tg257225-oss/TKL-Keyboard/Assets/new usb receptacle.png

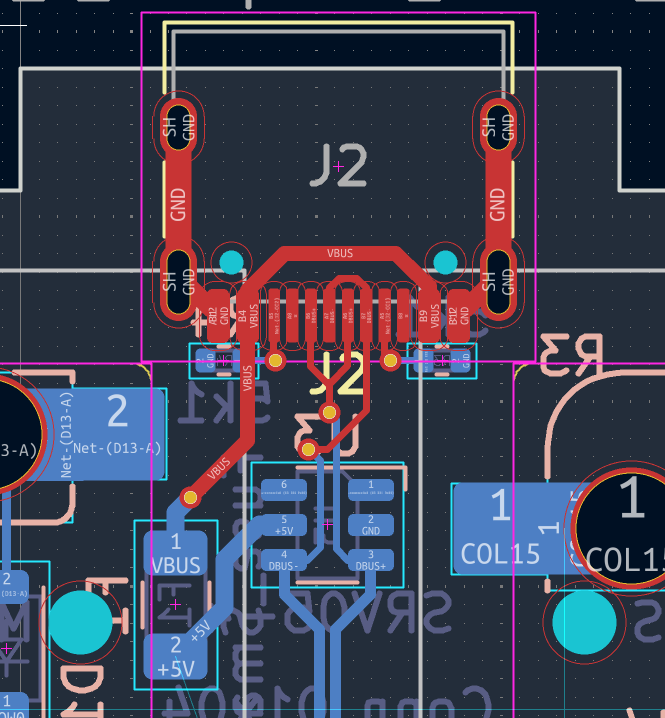
Assets/new usb receptacle.png
