tg257225-oss/TKL-Keyboard/Assets/plate sketch.png

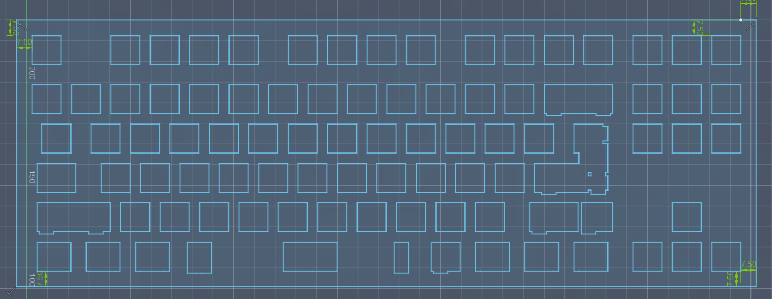
Assets/plate sketch.png
