tg257225-oss/TKL-Keyboard/Assets/rp2040.png

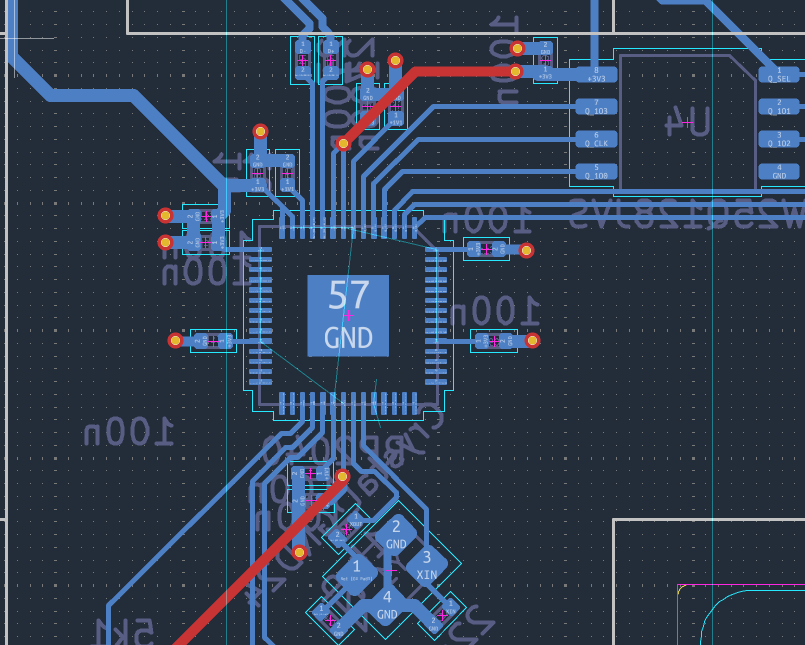
Assets/rp2040.png
