tg257225-oss/TKL-Keyboard/Assets/switch with silkscreens visible.png

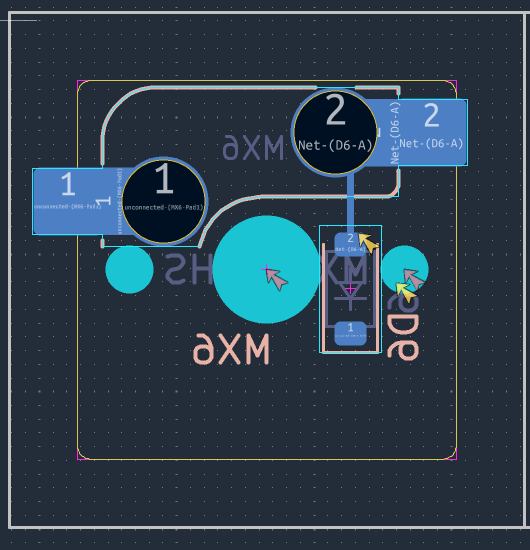
Assets/switch with silkscreens visible.png
