tg257225-oss/TKL-Keyboard/Assets/switch.png

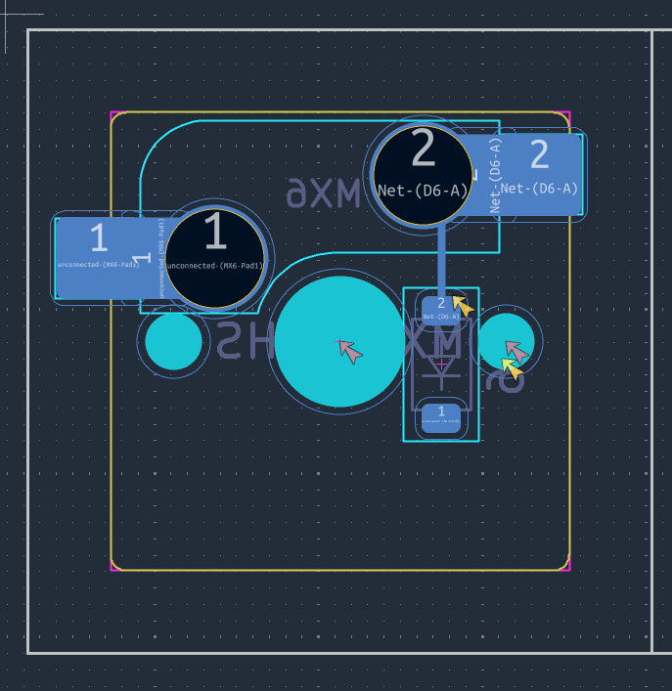
Assets/switch.png
