tg257225-oss/TKL-Keyboard/Assets/wired matrix to rp2040.png

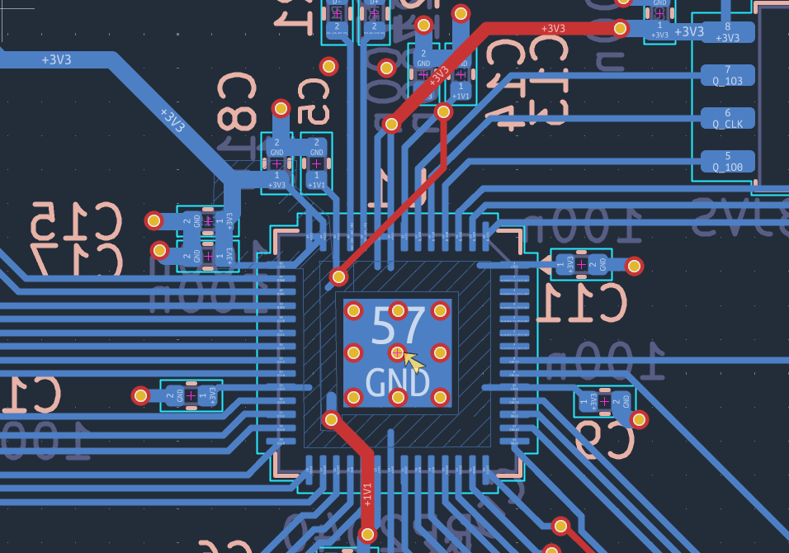
Assets/wired matrix to rp2040.png
