tg257225-oss/TKL-Keyboard/Assets/keyboardwiring.png

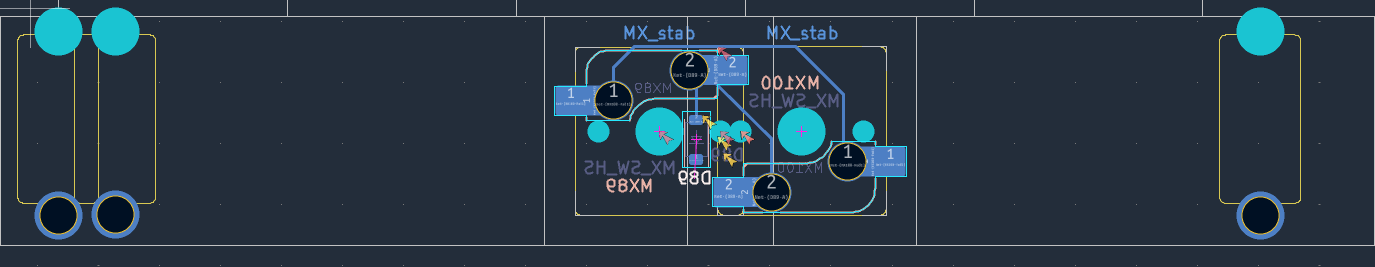
Assets/keyboardwiring.png
