tg257225-oss/TKL-Keyboard/Assets/coppa zone experimenting with settings.png

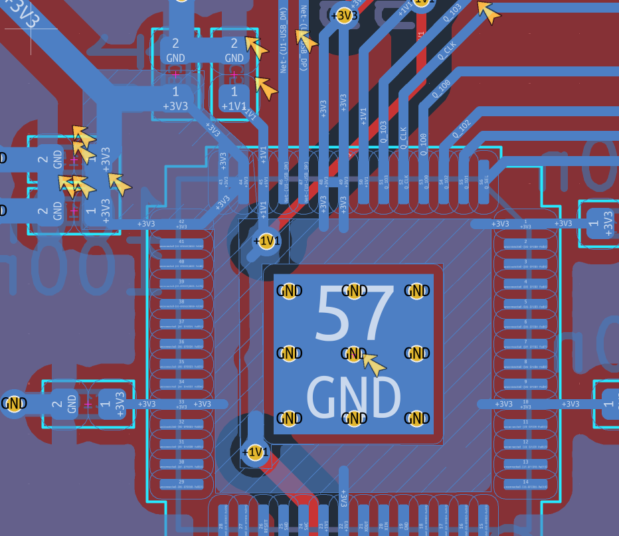
Assets/coppa zone experimenting with settings.png
