tg257225-oss/TKL-Keyboard/PCB/TKL.kicad_sch

## KiCad design PCB/TKL.kicad_sch (2026-07-12)

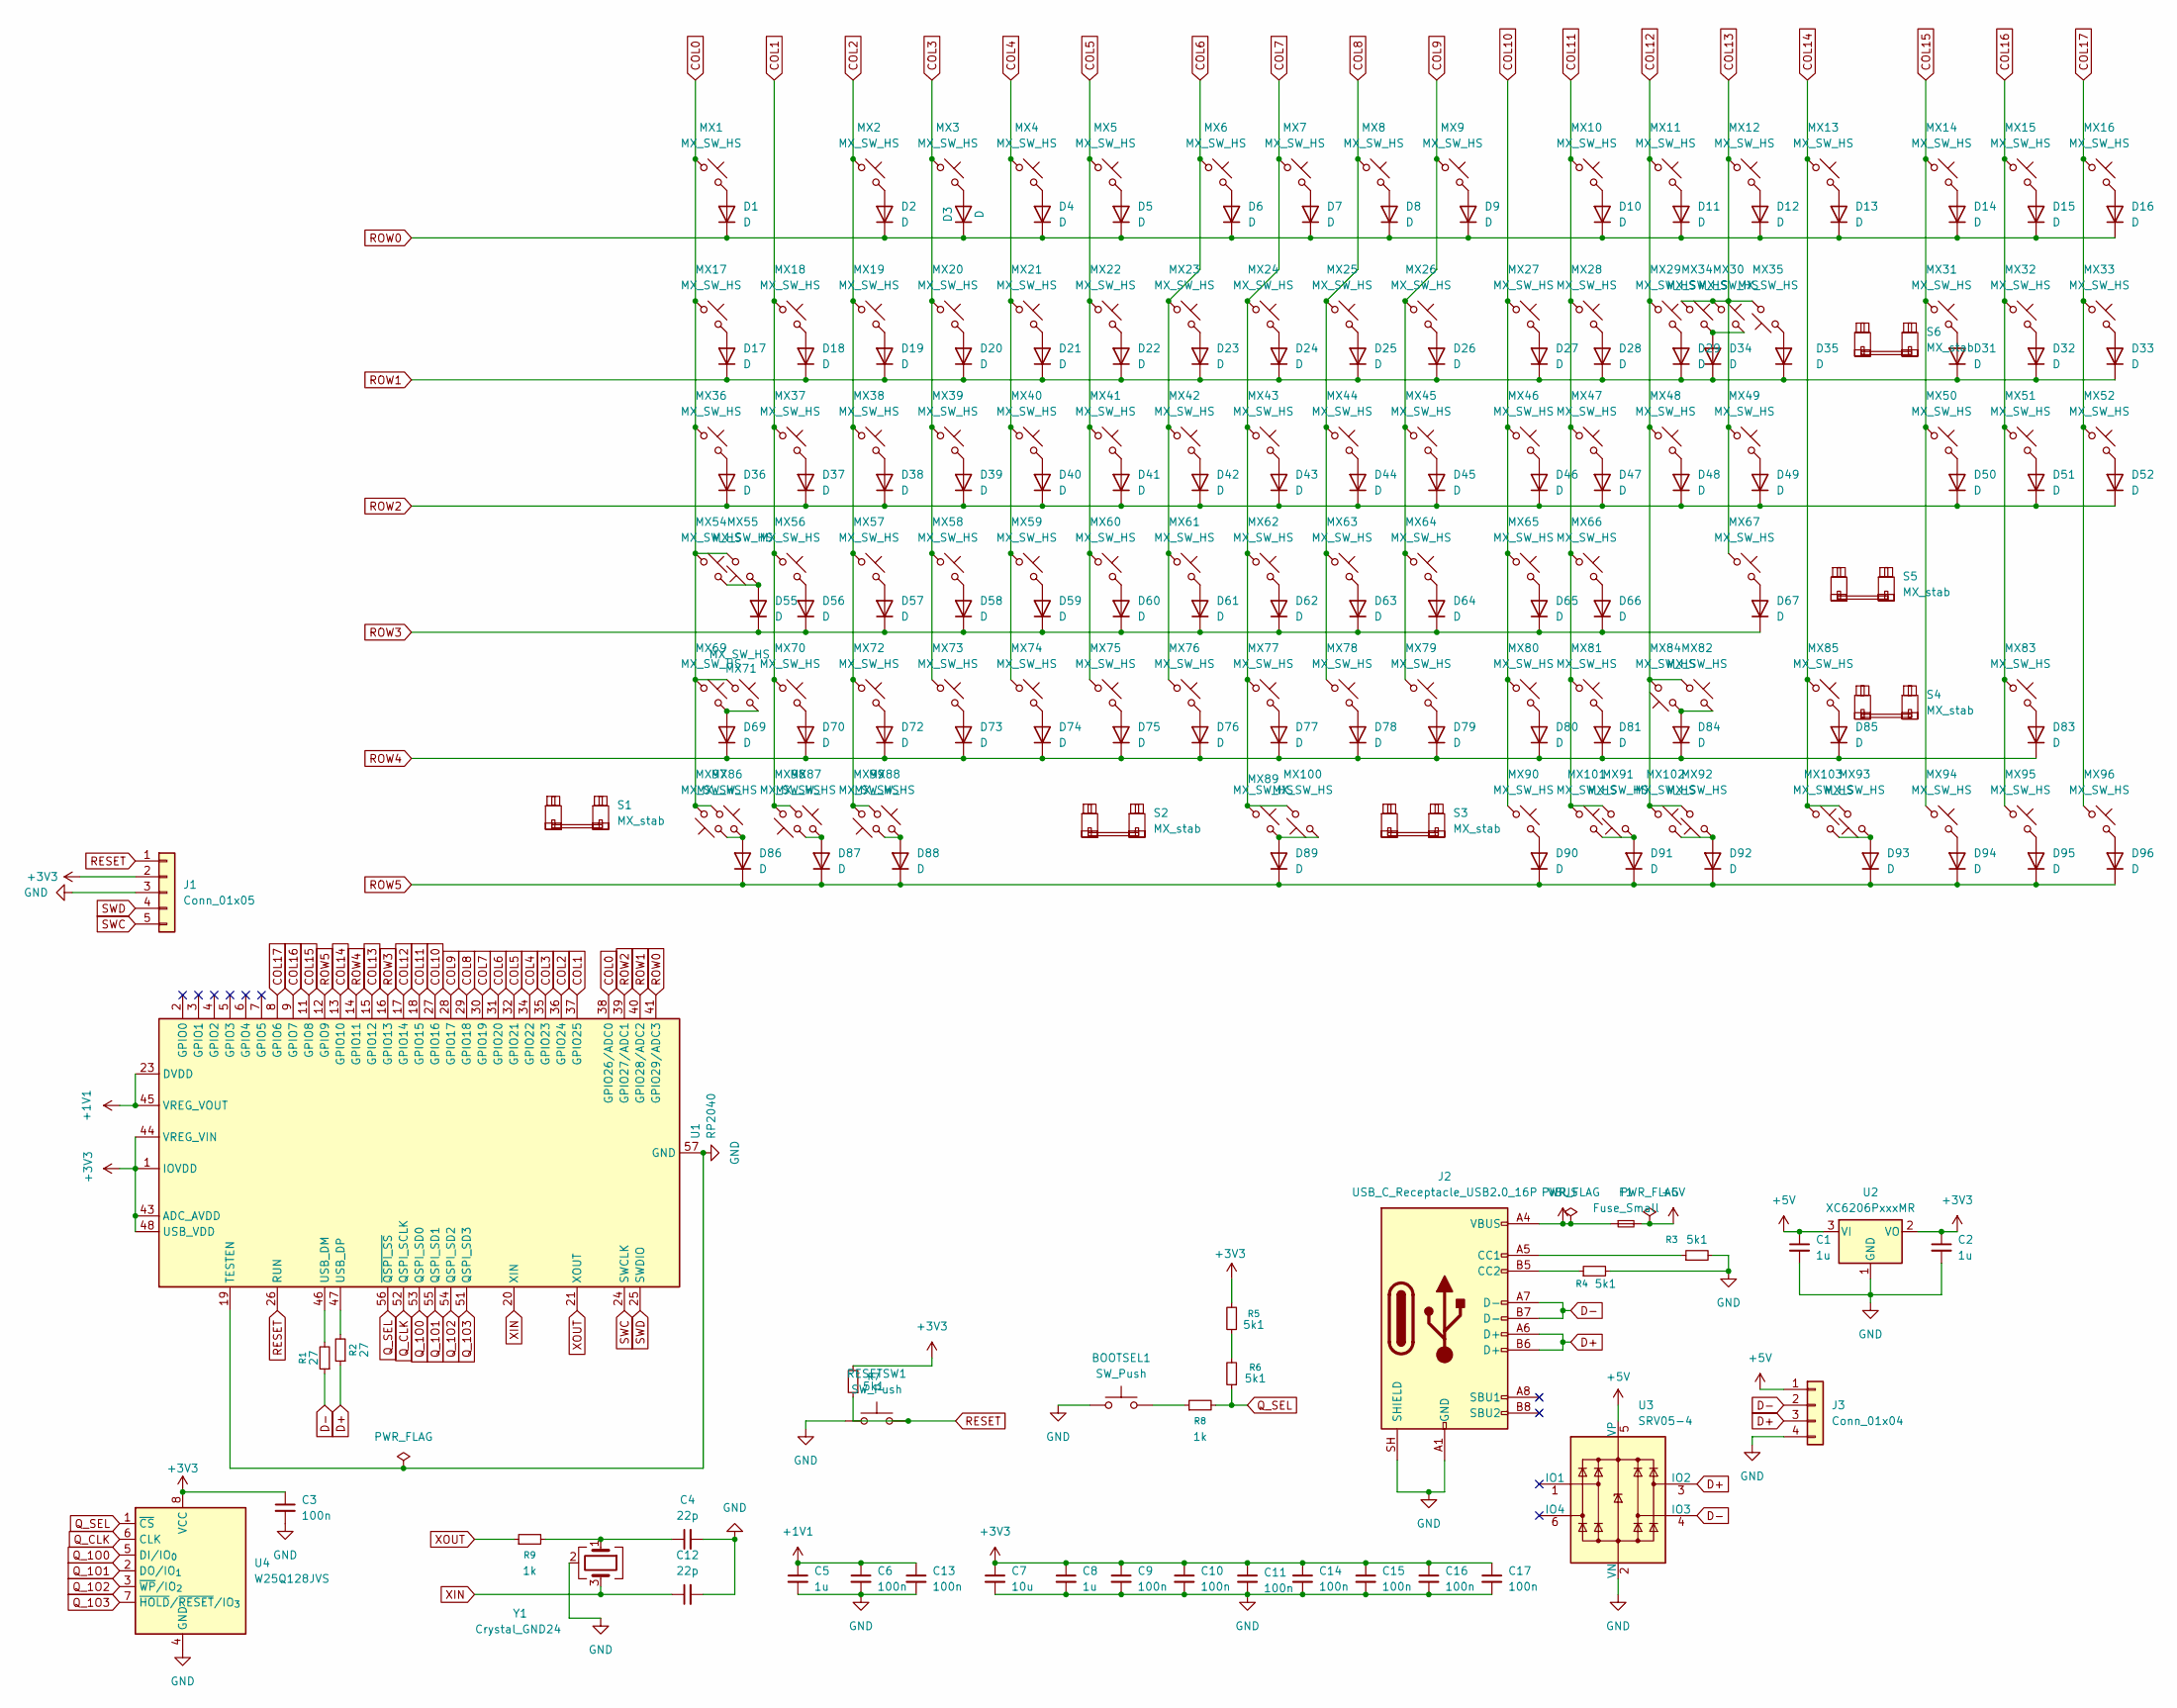
[picture p26: schematic TKL.kicad_sch]

Parts:
BOOTSEL1: SW_Push; SW_SPST_TL3342
C1, C2, C5, C8: 1u; C_0402_1005Metric
C3, C6, C9, C10, C11, C13, C14, C15, C16, C17: 100n; C_0402_1005Metric
C4, C12: 22p; C_0402_1005Metric
C7: 10u; C_0603_1608Metric
D1, D2, D3, D4, D5, D6, D7, D8, D9, D10, D11, D12, D13, D14, D15, D16, D17, D18, D19, D20, D21, D22, D23, D24, D25, D26, D27, D28, D29, D31, D32, D33, D34, D35, D36, D37, D38, D39, D40, D41, D42, D43, D44, D45, D46, D47, D48, D49, D50, D51, D52, D55, D56, D57, D58, D59, D60, D61, D62, D63, D64, D65, D66, D67, D69, D70, D72, D73, D74, D75, D76, D77, D78, D79, D80, D81, D83, D84, D85, D86, D87, D88, D89, D90, D91, D92, D93, D94, D95, D96: D; D_SOD-123
F1: Fuse_Small; Fuse_1206_3216Metric
J1: Conn_01x05; PinSocket_1x05_P2.54mm_Vertical
J2: USB_C_Receptacle_USB2.0_16P; USB_C_Receptacle_HRO_TYPE-C-31-M-12
J3: Conn_01x04; JST_SH_SM04B-SRSS-TB_1x04-1MP_P1.00mm_Horizontal
MX1, MX2, MX3, MX4, MX5, MX6, MX7, MX8, MX9, MX10, MX11, MX12, MX13, MX14, MX15, MX16, MX17, MX18, MX19, MX20, MX21, MX22, MX23, MX24, MX25, MX26, MX27, MX28, MX29, MX30, MX31, MX32, MX33, MX34, MX35, MX37, MX38, MX39, MX40, MX41, MX42, MX43, MX44, MX45, MX46, MX47, MX48, MX50, MX51, MX52, MX56, MX57, MX58, MX59, MX60, MX61, MX62, MX63, MX64, MX65, MX66, MX67, MX70, MX71, MX72, MX73, MX74, MX75, MX76, MX77, MX78, MX79, MX80, MX81, MX82, MX83, MX85, MX89, MX94, MX95, MX96, MX98, MX100, MX102: MX_SW_HS; SW_MX_HS_CPG151101S11_1u
MX36, MX49, MX97, MX99, MX101, MX103: MX_SW_HS; SW_MX_HS_CPG151101S11_1.5u
MX54: MX_SW_HS; SW_MX_HS_CPG151101S11_1.75u_STP_1.25
MX55, MX84: MX_SW_HS; SW_MX_HS_CPG151101S11_1.75u
MX69, MX86, MX87, MX88, MX90, MX91, MX92, MX93: MX_SW_HS; SW_MX_HS_CPG151101S11_1.25u
R1, R2: 27; R_0402_1005Metric
R3, R4, R5, R6, R7: 5k1; R_0402_1005Metric
R8, R9: 1k; R_0402_1005Metric
RESETSW1: SW_Push; SW_SPST_TL3342
S1, S5: MX_stab; STAB_MX_P_2.25u
S2: MX_stab; STAB_MX_P_6.25u
S3: MX_stab; STAB_MX_P_7u
S4: MX_stab; STAB_MX_P_2.75u
S6: MX_stab; STAB_MX_P_2u
U1: RP2040; QFN-56-1EP_7x7mm_P0.4mm_EP3.2x3.2mm
U2: XC6206PxxxMR; SOT-23-3
U3: SRV05-4; SOT-23-6-routable
U4: W25Q128JVS; SOIC-8_5.3x5.3mm_P1.27mm
Y1: Crystal_GND24; Crystal_SMD_3225-4Pin_3.2x2.5mm

Connections:
+1V1: C5.1, C6.1, C13.1, U1.23 (DVDD), U1.45 (VREG_VOUT), U1.50 (DVDD)
+3V3: C2.1, C3.1, C7.1, C8.1, C9.1, C10.1, C11.1, C14.1, C15.1, C16.1, C17.1, J1.2, R5.2, R7.2, U1.1 (IOVDD), U1.10 (IOVDD), U1.22 (IOVDD), U1.33 (IOVDD), U1.42 (IOVDD), U1.43 (ADC_AVDD), U1.44 (VREG_VIN), U1.48 (USB_VDD), U1.49 (IOVDD), U2.2 (VO), U4.8 (VCC)
+5V: C1.1, F1.2, J3.1, U2.3 (VI), U3.5 (VP)
COL0: MX1.1, MX17.1, MX36.1, MX54.1, MX55.2, MX69.1, MX71.2, MX86.1, MX97.2, U1.38 (GPIO26/ADC0)
COL1: MX18.1, MX37.1, MX56.1, MX70.1, MX87.1, MX98.2, U1.37 (GPIO25)
COL2: MX2.1, MX19.1, MX38.1, MX57.1, MX72.1, MX88.1, MX99.2, U1.36 (GPIO24)
COL3: MX3.1, MX20.1, MX39.1, MX58.1, MX73.1, U1.35 (GPIO23)
COL4: MX4.1, MX21.1, MX40.1, MX59.1, MX74.1, U1.34 (GPIO22)
COL5: MX5.1, MX22.1, MX41.1, MX60.1, MX75.1, U1.32 (GPIO21)
COL6: MX6.1, MX23.1, MX42.1, MX61.1, MX76.1, U1.31 (GPIO20)
COL7: MX7.1, MX24.1, MX43.1, MX62.1, MX77.1, MX89.1, MX100.2, U1.30 (GPIO19)
COL8: MX8.1, MX25.1, MX44.1, MX63.1, MX78.1, U1.29 (GPIO18)
COL9: MX9.1, MX26.1, MX45.1, MX64.1, MX79.1, U1.28 (GPIO17)
COL10: MX27.1, MX46.1, MX65.1, MX80.1, MX90.1, U1.27 (GPIO16)
COL11: MX10.1, MX28.1, MX47.1, MX66.1, MX81.1, MX91.2, MX101.1, U1.18 (GPIO15)
COL12: MX11.1, MX29.1, MX48.1, MX82.1, MX84.2, MX92.2, MX102.1, U1.17 (GPIO14)
COL13: MX12.1, MX30.1, MX34.1, MX35.2, MX49.1, MX67.1, U1.15 (GPIO12)
COL14: MX13.1, MX85.1, MX93.2, MX103.1, U1.13 (GPIO10)
COL15: MX14.1, MX31.1, MX50.1, MX94.1, U1.11 (GPIO8)
COL16: MX15.1, MX32.1, MX51.1, MX83.1, MX95.1, U1.9 (GPIO7)
COL17: MX16.1, MX33.1, MX52.1, MX96.1, U1.8 (GPIO6)
D+: J2.A6 (D+), J2.B6 (D+), J3.3, R2.1, U3.3 (IO2)
D-: J2.A7 (D-), J2.B7 (D-), J3.2, R1.1, U3.4 (IO3)
GND: BOOTSEL1.1, C1.2, C2.2, C3.2, C4.2, C5.2, C6.2, C7.2, C8.2, C9.2, C10.2, C11.2, C12.2, C13.2, C14.2, C15.2, C16.2, C17.2, J1.3, J2.A1 (GND), J2.A12 (GND), J2.B1 (GND), J2.B12 (GND), J2.SH (SHIELD), J3.4, R3.2, R4.2, RESETSW1.1, U1.19 (TESTEN), U1.57 (GND), U2.1 (GND), U3.2 (VN), U4.4 (GND), Y1.2 (G), Y1.4 (G)
unnamed: BOOTSEL1.2, R8.1
unnamed: C4.1, R9.2, Y1.1
unnamed: D1.2 (A), MX1.2
unnamed: D2.2 (A), MX2.2
unnamed: D3.2 (A), MX3.2
unnamed: D4.2 (A), MX4.2
unnamed: D5.2 (A), MX5.2
unnamed: D6.2 (A), MX6.2
unnamed: D7.2 (A), MX7.2
unnamed: D8.2 (A), MX8.2
unnamed: D9.2 (A), MX9.2
unnamed: D10.2 (A), MX10.2
unnamed: D11.2 (A), MX11.2
unnamed: D12.2 (A), MX12.2
unnamed: D13.2 (A), MX13.2
unnamed: D14.2 (A), MX14.2
unnamed: D15.2 (A), MX15.2
unnamed: D16.2 (A), MX16.2
unnamed: D17.2 (A), MX17.2
unnamed: D18.2 (A), MX18.2
unnamed: D19.2 (A), MX19.2
unnamed: D20.2 (A), MX20.2
unnamed: D21.2 (A), MX21.2
unnamed: D22.2 (A), MX22.2
unnamed: D23.2 (A), MX23.2
unnamed: D24.2 (A), MX24.2
unnamed: D25.2 (A), MX25.2
unnamed: D26.2 (A), MX26.2
unnamed: D27.2 (A), MX27.2
unnamed: D28.2 (A), MX28.2
unnamed: D29.2 (A), MX29.2
unnamed: D31.2 (A), MX31.2
unnamed: D32.2 (A), MX32.2
unnamed: D33.2 (A), MX33.2
unnamed: D34.2 (A), MX30.2, MX34.2
unnamed: D35.2 (A), MX35.1
unnamed: D36.2 (A), MX36.2
unnamed: D37.2 (A), MX37.2
unnamed: D38.2 (A), MX38.2
unnamed: D39.2 (A), MX39.2
unnamed: D40.2 (A), MX40.2
unnamed: D41.2 (A), MX41.2
unnamed: D42.2 (A), MX42.2
unnamed: D43.2 (A), MX43.2
unnamed: D44.2 (A), MX44.2
unnamed: D45.2 (A), MX45.2
unnamed: D46.2 (A), MX46.2
unnamed: D47.2 (A), MX47.2
unnamed: D48.2 (A), MX48.2
unnamed: D49.2 (A), MX49.2
unnamed: D50.2 (A), MX50.2
unnamed: D51.2 (A), MX51.2
unnamed: D52.2 (A), MX52.2
unnamed: D55.2 (A), MX54.2, MX55.1
unnamed: D56.2 (A), MX56.2
unnamed: D57.2 (A), MX57.2
unnamed: D58.2 (A), MX58.2
unnamed: D59.2 (A), MX59.2
unnamed: D60.2 (A), MX60.2
unnamed: D61.2 (A), MX61.2
unnamed: D62.2 (A), MX62.2
unnamed: D63.2 (A), MX63.2
unnamed: D64.2 (A), MX64.2
unnamed: D65.2 (A), MX65.2
unnamed: D66.2 (A), MX66.2
unnamed: D67.2 (A), MX67.2
unnamed: D69.2 (A), MX69.2, MX71.1
unnamed: D70.2 (A), MX70.2
unnamed: D72.2 (A), MX72.2
unnamed: D73.2 (A), MX73.2
unnamed: D74.2 (A), MX74.2
unnamed: D75.2 (A), MX75.2
unnamed: D76.2 (A), MX76.2
unnamed: D77.2 (A), MX77.2
unnamed: D78.2 (A), MX78.2
unnamed: D79.2 (A), MX79.2
unnamed: D80.2 (A), MX80.2
unnamed: D81.2 (A), MX81.2
unnamed: D83.2 (A), MX83.2
unnamed: D84.2 (A), MX82.2, MX84.1
unnamed: D85.2 (A), MX85.2
unnamed: D86.2 (A), MX86.2, MX97.1
unnamed: D87.2 (A), MX87.2, MX98.1
unnamed: D88.2 (A), MX88.2, MX99.1
unnamed: D89.2 (A), MX89.2, MX100.1
unnamed: D90.2 (A), MX90.2
unnamed: D91.2 (A), MX91.1, MX101.2
unnamed: D92.2 (A), MX92.1, MX102.2
unnamed: D93.2 (A), MX93.1, MX103.2
unnamed: D94.2 (A), MX94.2
unnamed: D95.2 (A), MX95.2
unnamed: D96.2 (A), MX96.2
unnamed: J2.A5 (CC1), R3.1
unnamed: J2.B5 (CC2), R4.1
unnamed: R1.2, U1.46 (USB_DM)
unnamed: R2.2, U1.47 (USB_DP)
unnamed: R5.1, R6.2
Q_1O0: U1.53 (QSPI_SD0), U4.5 (DI/IO_{0})
Q_1O1: U1.55 (QSPI_SD1), U4.2 (DO/IO_{1})
Q_1O2: U1.54 (QSPI_SD2), U4.3 (~WP/IO_{2})
Q_1O3: U1.51 (QSPI_SD3), U4.7 (~HOLD/~RESET/IO_{3})
Q_CLK: U1.52 (QSPI_SCLK), U4.6 (CLK)
Q_SEL: R6.1, R8.2, U1.56 (~QSPI_SS), U4.1 (~CS)
RESET: J1.1, R7.1, RESETSW1.2, U1.26 (RUN)
ROW0: D1.1 (K), D2.1 (K), D3.1 (K), D4.1 (K), D5.1 (K), D6.1 (K), D7.1 (K), D8.1 (K), D9.1 (K), D10.1 (K), D11.1 (K), D12.1 (K), D13.1 (K), D14.1 (K), D15.1 (K), D16.1 (K), U1.41 (GPIO29/ADC3)
ROW1: D17.1 (K), D18.1 (K), D19.1 (K), D20.1 (K), D21.1 (K), D22.1 (K), D23.1 (K), D24.1 (K), D25.1 (K), D26.1 (K), D27.1 (K), D28.1 (K), D29.1 (K), D31.1 (K), D32.1 (K), D33.1 (K), D34.1 (K), D35.1 (K), U1.40 (GPIO28/ADC2)
ROW2: D36.1 (K), D37.1 (K), D38.1 (K), D39.1 (K), D40.1 (K), D41.1 (K), D42.1 (K), D43.1 (K), D44.1 (K), D45.1 (K), D46.1 (K), D47.1 (K), D48.1 (K), D49.1 (K), D50.1 (K), D51.1 (K), D52.1 (K), U1.39 (GPIO27/ADC1)
ROW3: D55.1 (K), D56.1 (K), D57.1 (K), D58.1 (K), D59.1 (K), D60.1 (K), D61.1 (K), D62.1 (K), D63.1 (K), D64.1 (K), D65.1 (K), D66.1 (K), D67.1 (K), U1.16 (GPIO13)
ROW4: D69.1 (K), D70.1 (K), D72.1 (K), D73.1 (K), D74.1 (K), D75.1 (K), D76.1 (K), D77.1 (K), D78.1 (K), D79.1 (K), D80.1 (K), D81.1 (K), D83.1 (K), D84.1 (K), D85.1 (K), U1.14 (GPIO11)
ROW5: D86.1 (K), D87.1 (K), D88.1 (K), D89.1 (K), D90.1 (K), D91.1 (K), D92.1 (K), D93.1 (K), D94.1 (K), D95.1 (K), D96.1 (K), U1.12 (GPIO9)
SWC: J1.5, U1.24 (SWCLK)
SWD: J1.4, U1.25 (SWDIO)
VBUS: F1.1, J2.A4 (VBUS), J2.A9 (VBUS), J2.B4 (VBUS), J2.B9 (VBUS)
XIN: C12.1, U1.20 (XIN), Y1.3
XOUT: R9.1, U1.21 (XOUT)
